cwsimmons/esdi_interface/software/crc.py

#   Copyright 2024 Christopher Simmons

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
def lsb32(payload, initial=0):
    if not isinstance(payload, bytes):
        raise TypeError()
    
    remainder = initial
    for x in payload:
        remainder = remainder ^ x

        for i in range(8):
            if (remainder & 0x01):
                # ethernet = 0xEDB88320
                remainder = (remainder >> 1) ^ 0x4440A051
            else:
                remainder = (remainder >> 1)
    return remainder

# 0x140A0445
# 0x4440A051

def msb32(payload, initial=0):
    if not isinstance(payload, bytes):
        raise TypeError()
    
    remainder = initial
    for x in payload:
        remainder = remainder ^ (x << 24)

        for i in range(8):
            if (remainder & 0x80000000):
                # 0x04C11DB7 == Ethernet
                remainder = ((remainder << 1) & 0xFFFFFFFF) ^ 0x41044185
            else:
                remainder = ((remainder << 1) & 0xFFFFFFFF)
    return remainder



def msb16(payload, initial=0):
    if not isinstance(payload, bytes):
        raise TypeError()
    
    remainder = initial
    for x in payload:
        remainder = remainder ^ (x << 8)

        for i in range(8):
            if (remainder & 0x8000):
                remainder = ((remainder << 1) & 0xFFFF) ^ 0x1021
            else:
                remainder = ((remainder << 1) & 0xFFFF)
    return remainder


data = [0x00, 0x09, 0x03, 0x08]

# An RT sector
sector = [
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

# Data Area
# reveng.exe -s -w 32 -f s4.bin s7.bin s8.bin s9.bin
# width=32  poly=0x140a0445  init=0x00000000  refin=false  refout=false  xorout=0x00000000  check=0x86aceee1  residue=0x00000000  name=(none)
